igiannakas/mmWave-Presense-Sensor-D1-Mini-DFRobot-/project-images/4.jpeg

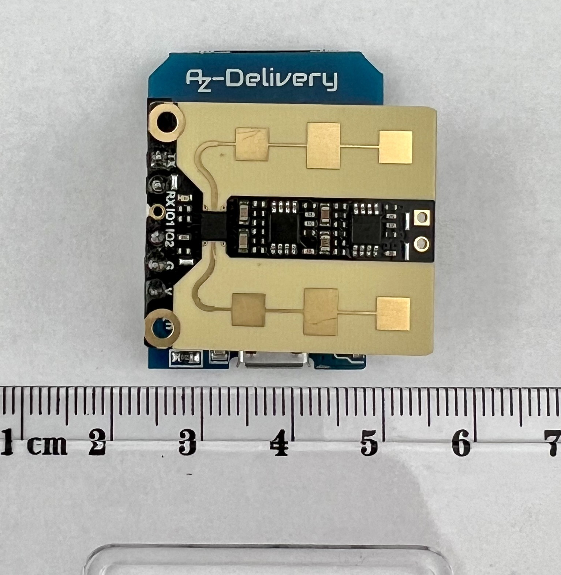
project-images/4.jpeg
